veroxzik/bemani-arduino-boards/Firmware/Micro-Bemani-HID/Globals.h

#ifndef __GLOBALS_H__
#define __GLOBALS_H__

#include "Config.h"

/* --- --- --- --- --- --- --- ---
   Settings that do not need to be changed
   --- --- --- --- --- --- --- --- */

#if NUM_ENCODERS > 2
#error "More than 2 encoder cannot be defined"
#endif

#if defined(USE_MICRO)

// Pins for the buttons
// If using the breakout boards, these aleady in the correct order to correspond with B1-B12.
uint8_t numButtons = (12 - NUM_ENCODERS);
uint8_t buttonPins[] = {12, 10, 8, 6, 4, SS, 13, A2, A4, MISO, 1, 2};
uint8_t ledPins[] = {11, 9, 7, 5, MOSI, A0, A1, A3, A5, SCK, 0, 3};

// Pins for the Encoders
// QE1 is pins 0 and 1
// QE2 is pins 2 and 3
// These cannot be changed, as they are linked to interrupt pins.
uint8_t encoderPins[] = {2, 3, 0, 1};
#define NUM_SINGLE_LED (12 - NUM_ENCODERS)

#elif defined(USE_MICRORGB)

// Pins for the buttons
// If using the breakout boards, these aleady in the correct order to correspond with B1-B11.
uint8_t numButtons = (11 - NUM_ENCODERS);
uint8_t buttonPins[] = {12, 10, 8, 6, 4, SS, 13, A2, A4, 1, 2};
uint8_t ledPins[] = {11, 9, 7, 5, MISO, A0, A1, A3, A5, 0, 3};

// Pins for the Encoders
// QE1 is pins 0 and 1
// QE2 is pins 2 and 3
// These cannot be changed, as they are linked to interrupt pins.
uint8_t encoderPins[] = {2, 3, 0, 1};
#define NUM_SINGLE_LED (11 - NUM_ENCODERS)

#elif defined(USE_MICRORGB_V1_2)

// Pins for the buttons
// If using the breakout boards, these aleady in the correct order to correspond with B1-B11.
uint8_t numButtons = (11 - NUM_ENCODERS);
uint8_t buttonPins[] = {12, 10, 8, 6, 4, A4, 13, A2, MISO, 1, 2};
uint8_t ledPins[] = {11, 9, 7, 5, A5, A0, A1, A3, SS, 0, 3};

// Pins for the Encoders
// QE1 is pins 0 and 1
// QE2 is pins 2 and 3
// These cannot be changed, as they are linked to interrupt pins.
uint8_t encoderPins[] = {2, 3, 0, 1};
#define NUM_SINGLE_LED (11 - NUM_ENCODERS)

#elif defined(USE_PROMICRO)
// Pins for the buttons
// If using the breakout boards, these aleady in the correct order to correspond with B1-B9.
uint8_t numButtons = (9 - NUM_ENCODERS);
uint8_t buttonPins[] = {20, 18, 14, 10, 5, 7, 9, 2, 1};
uint8_t ledPins[] = {21, 19, 15, 16, 4, 6, 8, 3, 0};
#define NUM_SINGLE_LED (9 - NUM_ENCODERS)

// Pins for the Encoders
// QE1 is pins 0 and 1
// QE2 is pins 2 and 3
// These cannot be changed, as they are linked to interrupt pins.
uint8_t encoderPins[] = {0, 1, 2, 3};

#else
#error "Board Not Defined in Confing.h"
#endif

// This board does not support RGB
#define NUM_RGB_LED 0

#endif
